ch0mik/A600_CrystalCase/dxf_screws/04_right_io_3mm.dxf

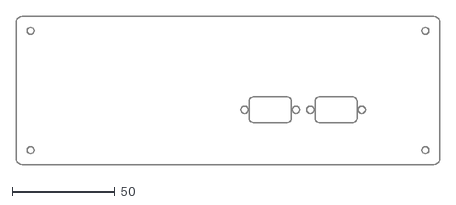
[picture p18: CAD file, 2026-08-17]
dxf_screws/04_right_io_3mm.dxf
206.0 x 72.0
